Dynix7/NFC-Card/assets/kicad.png

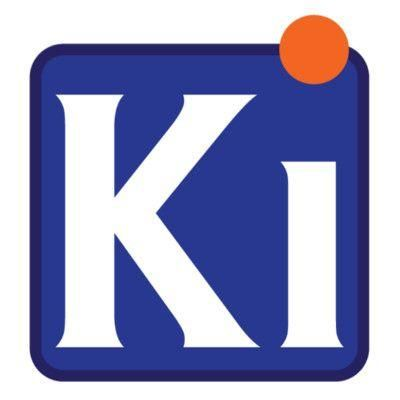
assets/kicad.png
