Dynix7/NFC-Card/assets/sig1.png

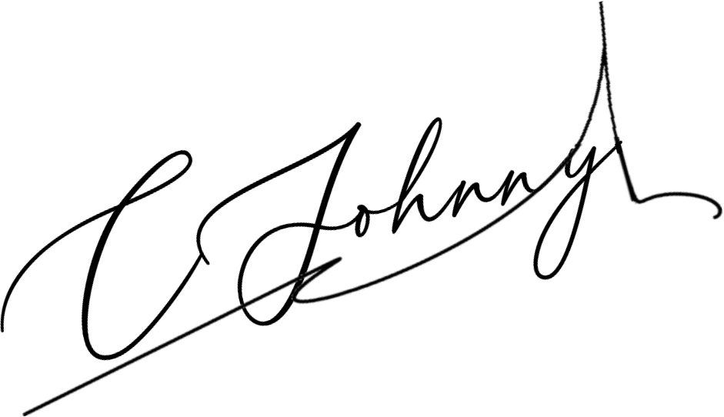
assets/sig1.png
